fread/visvitalis/docs/present/img/ram.pdf

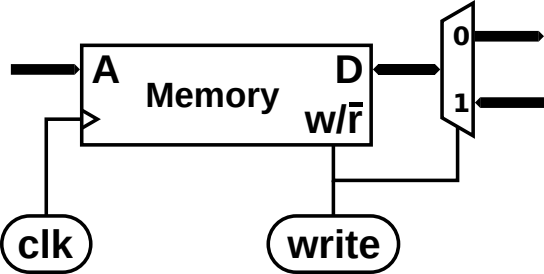
[picture p5: figure]
Memory A; clk; write
