fread/visvitalis/docs/present/img/register.pdf

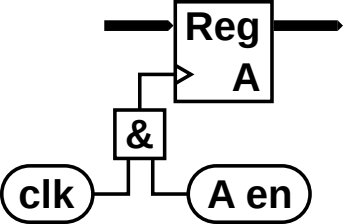
[picture p6: figure]
Reg A; clk
