fread/visvitalis/docs/present/img/sch-alu.pdf

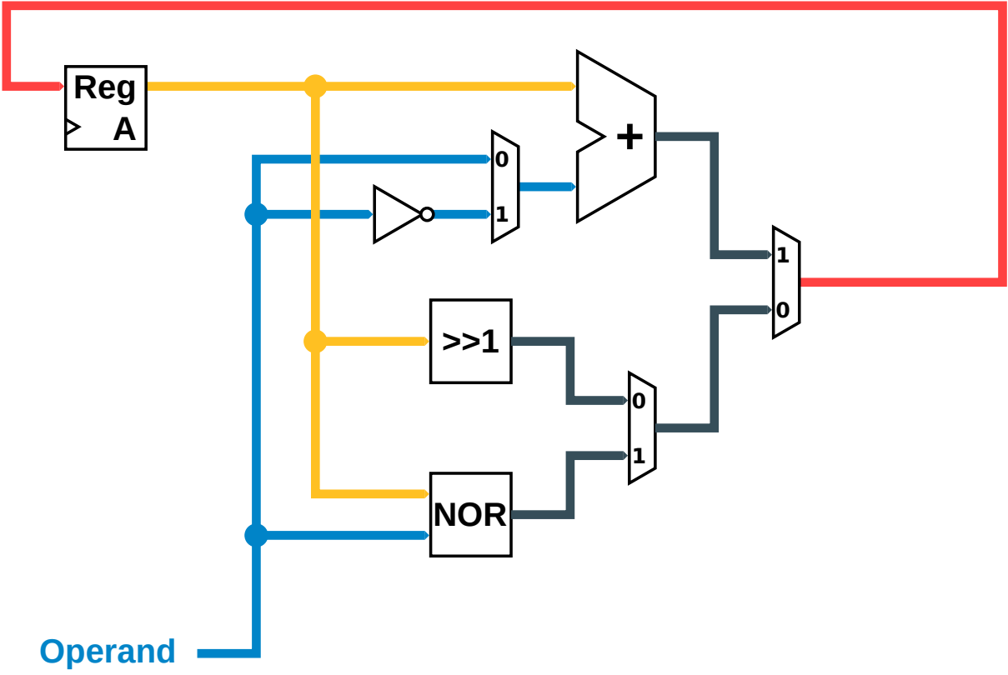
[picture p7: figure]
NOR; RegA; Operand
