fread/visvitalis/docs/present/img/sch-immediate.pdf

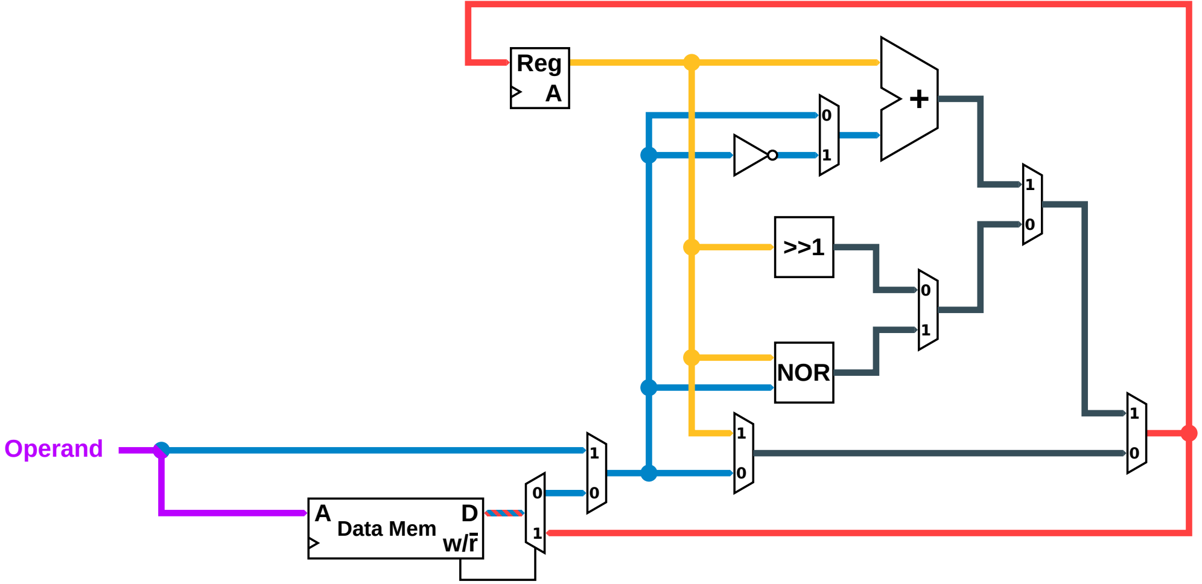
[picture p8: figure]
Data Mem A; NOR; RegA; Operand
