fread/visvitalis/docs/present/img/sch-load.pdf

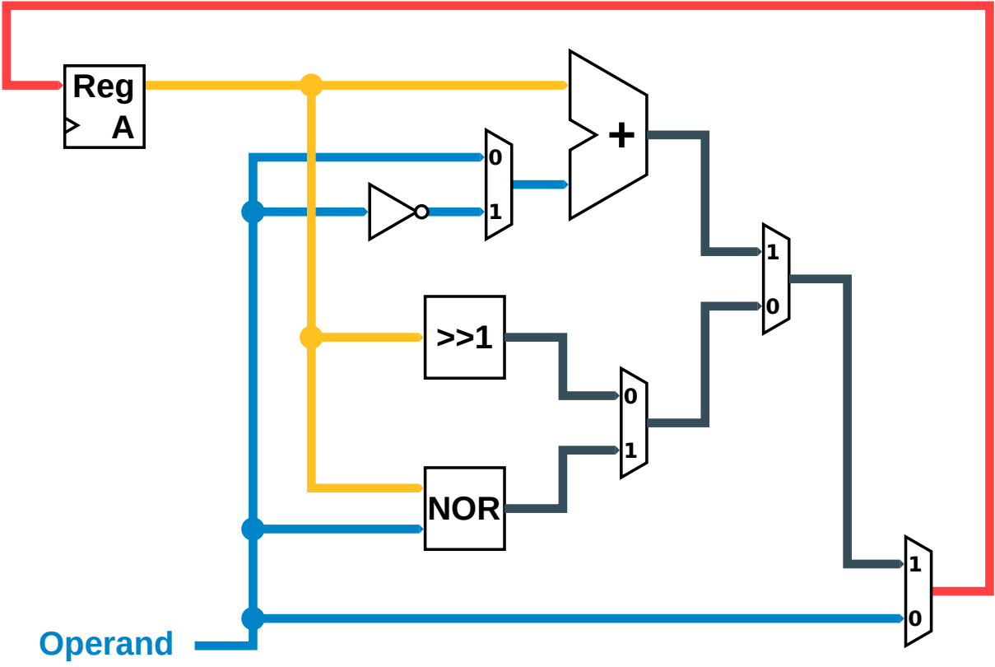
[picture p9: figure]
NOR; RegA; Operand
