fread/visvitalis/docs/present/img/sch-loadstore.pdf

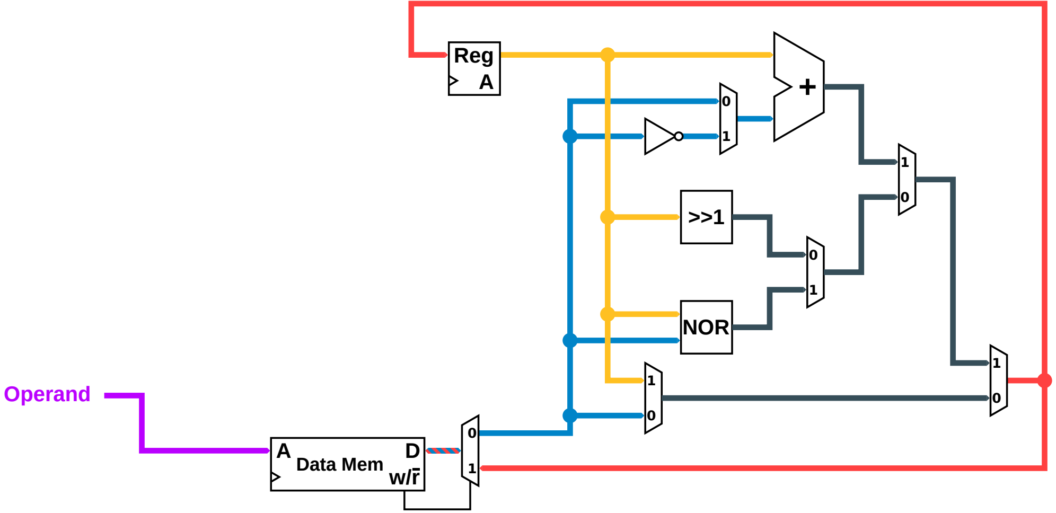
[picture p10: figure]
Data Mem A; NOR; RegA; Operand
