fread/visvitalis/docs/present/img/sch-pointer.pdf

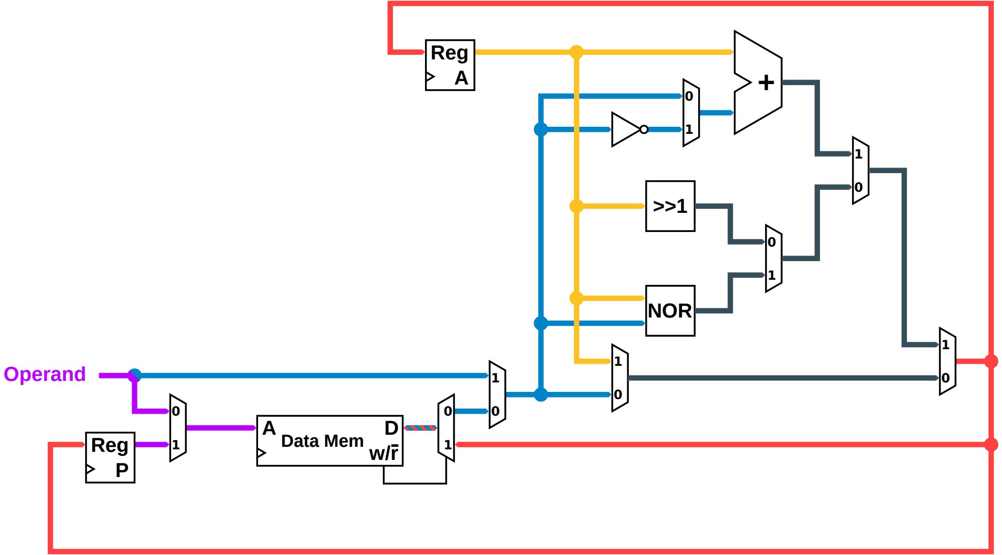
[picture p11: figure]
Data Mem A; NOR; RegA; RegP; Operand
