fread/visvitalis/docs/present/img/abc-formel.pdf

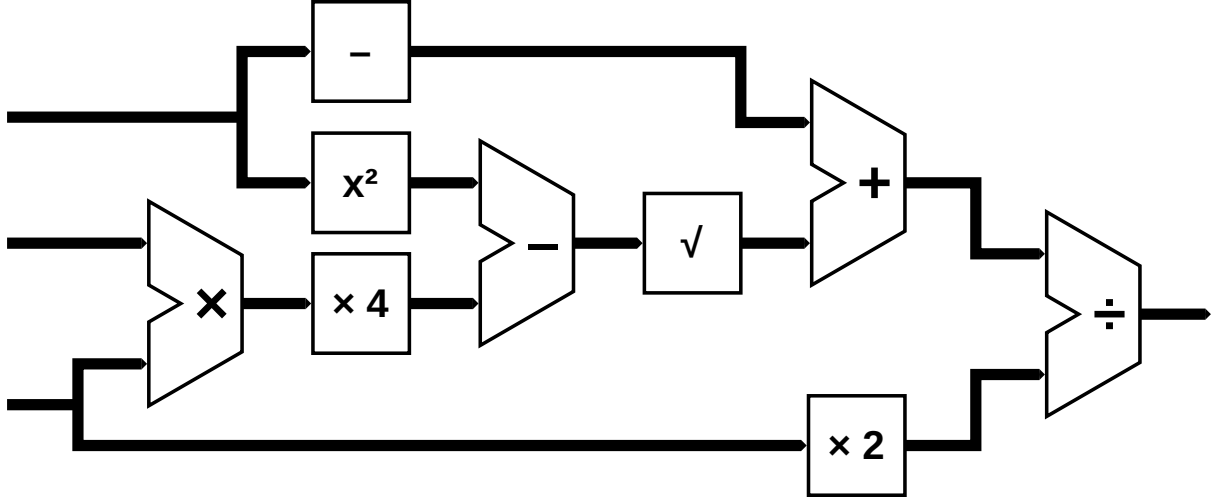
[picture p12: figure]

# bca

x
1
