fread/visvitalis/docs/present/img/ripple-carry.pdf

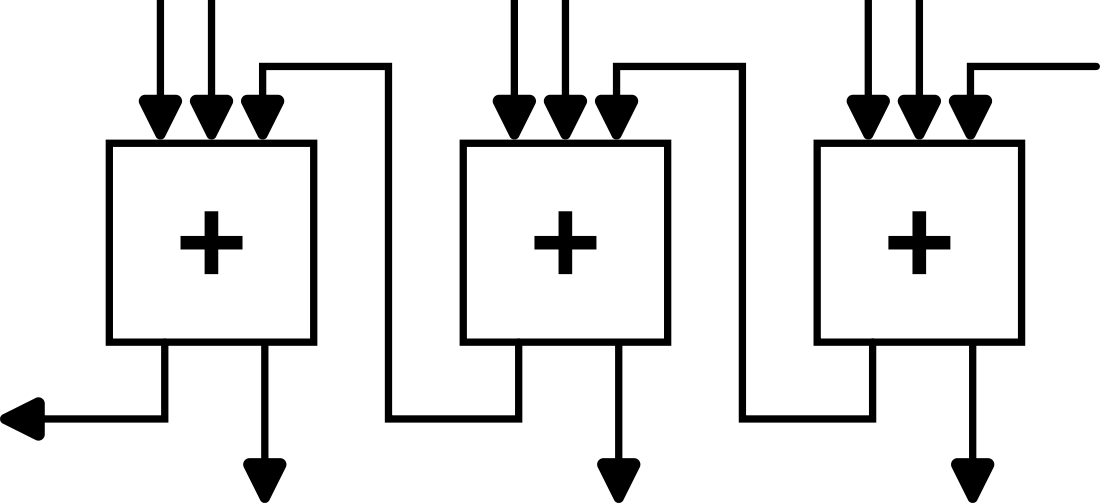
[picture p18: page 1]
