fread/visvitalis/docs/present/img/sch-controls.pdf

+

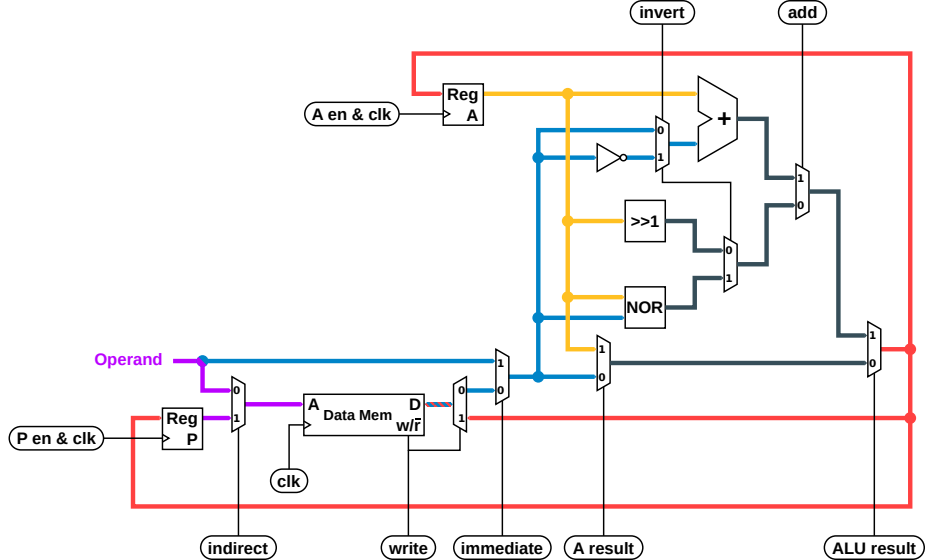
[picture p19: page 1]
Data Mem A; NOR; A en & clk; Reg A; clk; indirect; write; immediate; A result; ALU result; invert; add; Reg P; Operand; P en & clk
