fread/visvitalis/docs/present/img/title-slide.pdf

# andi ‹andi@entropia.de›

# Computer selbst bauen

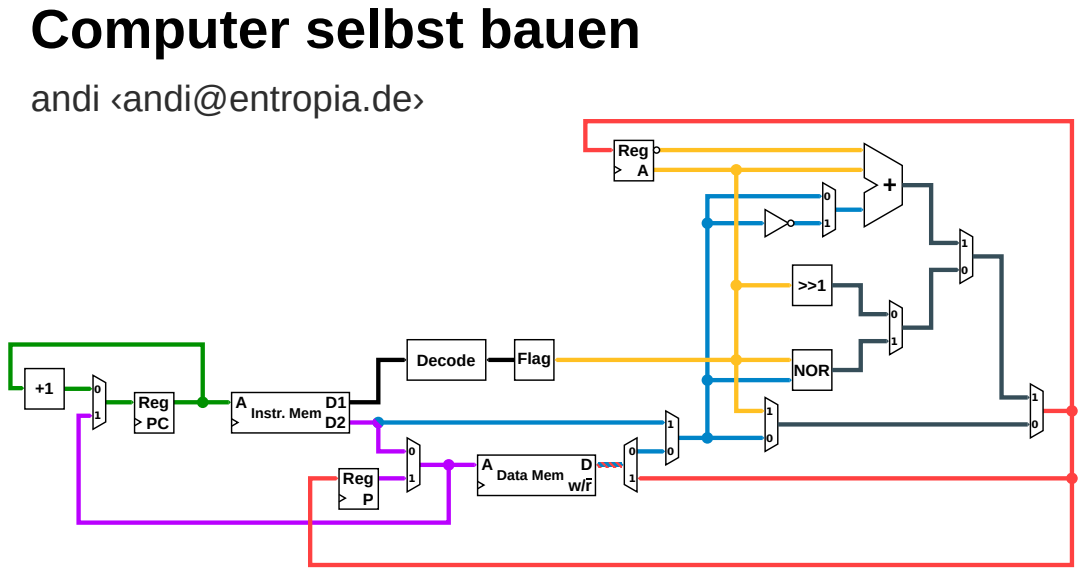
[picture p20: page 1]
Decode; Flag; Data Mem A; NOR; Reg A; Reg P; Instr. Mem A; Reg PC
