fread/visvitalis/mem-esp-firmware/main/memory_controller.cpp

#include "memory_controller.hpp"

#include <esp_log.h>

static const char *TAG = "MEMORY CONTROLLER";

MemoryController::MemoryController(Memory &memory, Drv8908 &output_driver)
	: memory(memory),
	  output_driver(output_driver)
{
	output_driver.set_high_z();
}

MemoryController::~MemoryController()
{
	output_driver.set_high_z();
}

void MemoryController::on_address_change(uint8_t new_address)
{
	ESP_LOGD(TAG, "new address %x", new_address);
	current_address = new_address;
	if (current_rw_state == RwState::READ) {
		ESP_LOGI(TAG, "R %02x = %04x", current_address, memory.read(current_address));
		output_driver.set_output(memory.read(current_address));
	}
}

void MemoryController::on_write_pin_change(RwState new_state)
{
	current_rw_state = new_state;

	if (current_rw_state == RwState::WRITE) {
		ESP_LOGD(TAG, "state: write");
		output_driver.set_high_z();
	} else {
		ESP_LOGD(TAG, "state: read");
		output_driver.set_output(memory.read(current_address));
	}
}

void MemoryController::on_write_cycle_complete(uint8_t new_data)
{
	ESP_LOGD(TAG, "write cycle %x", new_data);
	ESP_LOGI(TAG, "W %02x := %04x", current_address, new_data);
	memory.write(current_address, new_data);
}

void MemoryController::invalidate()
{
	if (current_rw_state == RwState::READ) {
		ESP_LOGI(TAG, "R %02x = %04x", current_address, memory.read(current_address));
		output_driver.set_output(memory.read(current_address));
	}
}
