fread/visvitalis/mem-esp-firmware/main/drv8908.hpp

#pragma once

#include <array>

#include <driver/gpio.h>
#include <driver/spi_master.h>

enum class BusMode {
	ONE_CHIP,
	TWO_CHIPS,
};

class Drv8908 {
private:
	spi_device_handle_t spi_device;
	gpio_num_t fault_pin;
	BusMode bus_mode;

	BusMode probe_bus_for_chip_count();

	void disable_open_load_detection();

	static void fault_pin_change_isr(void *arg);
	static void on_fault_pin_change(void *arg1, uint32_t level);
	void handle_fault();

	uint8_t transmit_one_chip(uint8_t address, uint8_t data);
	std::array<uint8_t, 2> transmit_two_chips(uint8_t address, uint8_t data);
	std::array<uint8_t, 2> transmit_two_chips(uint8_t address1, uint8_t data1, uint8_t address2, uint8_t data2);

	void set_h_bridges(uint32_t h_bridge_settings);

public:
	Drv8908(spi_host_device_t spi_host,
	        gpio_num_t chip_select_pin,
		gpio_num_t fault_pin);

	void set_output(uint16_t value);

	void set_high_z();

	void reset_fault();
};
